RemiFM/USB-LiDAR-VL53L9/pcb/3d/TLV73328PDBVR.stp

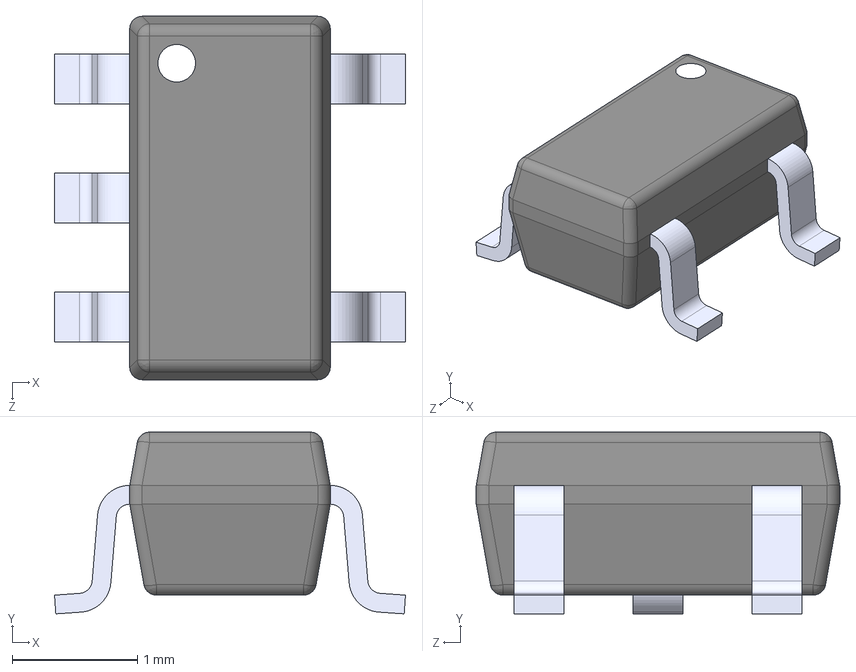
[picture p17: CAD file, 2026-06-27]
pcb/3d/TLV73328PDBVR.stp
2.80 x 1.45 x 2.90 mm
